alexanderenrique/e-ink-display/e-ink_code/firmware/apps/shelf/config.h

#ifndef SHELF_APP_CONFIG_H
#define SHELF_APP_CONFIG_H

// Shelf app configuration

// Default server host and port (can be overridden via BLE config)
#define SHELF_APP_DEFAULT_SERVER_HOST "192.168.1.100"
#define SHELF_APP_DEFAULT_SERVER_PORT 8080

#endif // SHELF_APP_CONFIG_H
