alexanderenrique/e-ink-display/e-ink_code/firmware/apps/fun/config.h

#ifndef FUN_APP_CONFIG_H
#define FUN_APP_CONFIG_H

// Fun app configuration
// Network and OTA constants are now in firmware/core/hardware_config.h
#include "../../core/hardware_config.h"

#endif // FUN_APP_CONFIG_H
