alexanderenrique/e-ink-display/e-ink_code/firmware/apps/shelf/app.cpp

#include "app.h"
#include "fetch.h"
#include "render.h"
#include "config.h"
#include "../../core/display/display_manager.h"
#include "../../core/power/power_manager.h"
#include "../../core/bluetooth/cold_start_ble.h"
#include "../../core/wifi/wifi_manager.h"

ShelfApp::ShelfApp() : _serverHost(SHELF_APP_DEFAULT_SERVER_HOST), _serverPort(SHELF_APP_DEFAULT_SERVER_PORT) {
}

bool ShelfApp::configure(const JsonObject& config) {
    Serial.println("[ShelfApp] Configuring Shelf App");

    if (config.containsKey("binId")) {
        _binId = config["binId"].as<const char*>();
        Serial.print("[ShelfApp] Bin ID: ");
        Serial.println(_binId);
    } else if (config.containsKey("bin_id")) {
        _binId = config["bin_id"].as<const char*>();
        Serial.print("[ShelfApp] Bin ID: ");
        Serial.println(_binId);
    }
    
    // Get server host (support both camelCase and snake_case)
    if (config.containsKey("serverHost")) {
        _serverHost = config["serverHost"].as<const char*>();
    } else if (config.containsKey("server_host")) {
        _serverHost = config["server_host"].as<const char*>();
    }
    // Fallback to default if not set
    if (_serverHost.length() == 0) {
        _serverHost = SHELF_APP_DEFAULT_SERVER_HOST;
    }
    
    // Get server port (support both camelCase and snake_case)
    if (config.containsKey("serverPort")) {
        _serverPort = config["serverPort"].as<uint16_t>();
    } else if (config.containsKey("server_port")) {
        _serverPort = config["server_port"].as<uint16_t>();
    } else {
        _serverPort = SHELF_APP_DEFAULT_SERVER_PORT;
    }
    
    // Legacy support: if serverUrl is provided, try to parse it
    if (config.containsKey("serverUrl") || config.containsKey("server_url")) {
        String serverUrl = config.containsKey("serverUrl") 
            ? config["serverUrl"].as<const char*>()
            : config["server_url"].as<const char*>();
        // Try to parse URL format: http://host:port or host:port
        int protocolEnd = serverUrl.indexOf("://");
        String hostPort = (protocolEnd >= 0) ? serverUrl.substring(protocolEnd + 3) : serverUrl;
        int colonPos = hostPort.indexOf(':');
        if (colonPos > 0) {
            _serverHost = hostPort.substring(0, colonPos);
            _serverPort = hostPort.substring(colonPos + 1).toInt();
        } else {
            _serverHost = hostPort;
        }
    }
    
    Serial.print("[ShelfApp] Server Host: ");
    Serial.println(_serverHost);
    Serial.print("[ShelfApp] Server Port: ");
    Serial.println(_serverPort);
    Serial.print("[ShelfApp] Server URL: ");
    Serial.println(buildServerUrl());

    if (config.containsKey("refreshInterval")) {
        _refreshIntervalMinutes = config["refreshInterval"].as<uint32_t>();
        if (_refreshIntervalMinutes < 1) _refreshIntervalMinutes = 1;
        Serial.print("[ShelfApp] Refresh interval: ");
        Serial.print(_refreshIntervalMinutes);
        Serial.println(" min");
    }

    return true;
}

bool ShelfApp::begin() {
    Serial.println("[ShelfApp] Starting Shelf App");
    
    // Initialize display
    if (_display) {
        _display->begin();
    }
    
    return true;
}

String ShelfApp::buildServerUrl() const {
    return "http://" + _serverHost + ":" + String(_serverPort);
}

void ShelfApp::loop() {
    // Get battery percentage
    int batteryPercent = -1;
    if (_power) {
        batteryPercent = _power->getBatteryPercentage();
    }
    
    // Try to connect WiFi if we have bin ID and server configured
    bool wifiConnected = false;
    if (_wifi && _binId.length() > 0 && _serverHost.length() > 0 && _serverPort > 0) {
        String wifiSSID = ColdStartBle::getStoredWiFiSSID();
        String wifiPassword = ColdStartBle::getStoredWiFiPassword();
        if (wifiSSID.length() > 0) {
            Serial.println("[ShelfApp] WiFi connection requested");
            wifiConnected = _wifi->begin(wifiSSID.c_str(), wifiPassword.c_str());
            if (wifiConnected) {
                Serial.println("[ShelfApp] WiFi connection successful - ready for server API calls");
            } else {
                Serial.println("[ShelfApp] WiFi connection failed - will show error");
            }
        } else {
            Serial.println("[ShelfApp] No WiFi credentials stored. Bin data cannot be fetched.");
        }
    }
    
    // Fetch shelf data
    String shelfData;
    if (_binId.length() > 0 && _serverHost.length() > 0 && _serverPort > 0 && wifiConnected) {
        String serverUrl = buildServerUrl();
        shelfData = fetchShelfData(_binId.c_str(), serverUrl.c_str());
    } else {
        if (_binId.length() == 0) {
            shelfData = "Shelf Label\nBin ID not configured";
        } else if (_serverHost.length() == 0 || _serverPort == 0) {
            shelfData = "Shelf Label\nServer not configured";
        } else {
            shelfData = "Shelf Label\nWiFi not connected";
        }
    }
    
    // Render shelf data
    if (_display) {
        renderShelfData(_display, shelfData, batteryPercent);
    }
    
    // Disable SPI after display update
    if (_display) {
        _display->disableSPI();
    }
    
    // Disable WiFi after fetching to save power
    if (_wifi) {
        _wifi->disconnect();
    }
    
    // Enter deep sleep until next cycle (or delay if no power manager)
    uint32_t sleepSeconds = _refreshIntervalMinutes * 60UL;
    if (_power) {
        Serial.print("[ShelfApp] Entering deep sleep for ");
        Serial.print(_refreshIntervalMinutes);
        Serial.println(" min");
        _power->enterDeepSleep(sleepSeconds);
    } else {
        delay(sleepSeconds * 1000UL);
    }
}

void ShelfApp::end() {
    Serial.println("[ShelfApp] Ending Shelf App");
    
    // Disable display
    if (_display) {
        _display->hibernate();
        _display->disableSPI();
    }
}
