alexanderenrique/e-ink-display/e-ink_code/firmware/apps/messages/render.cpp

#include "render.h"
#include "../../core/display/display_manager.h"

void renderMessages(DisplayManager* display, const String& text, int batteryPercent) {
    if (display == nullptr) return;
    display->displayTextOnly(text, batteryPercent);
}
