alexanderenrique/e-ink-display/e-ink_code/firmware/apps/sensor/render.cpp

#include "render.h"
#include "../../core/display/display_manager.h"

void renderSensorData(DisplayManager* display, String data, int batteryPercent) {
    if (display == nullptr) return;
    display->displayDefault(data, batteryPercent);
}
